greyboxaudio/Nyan-1073-EQ/eurorack_powerLayout.jpg

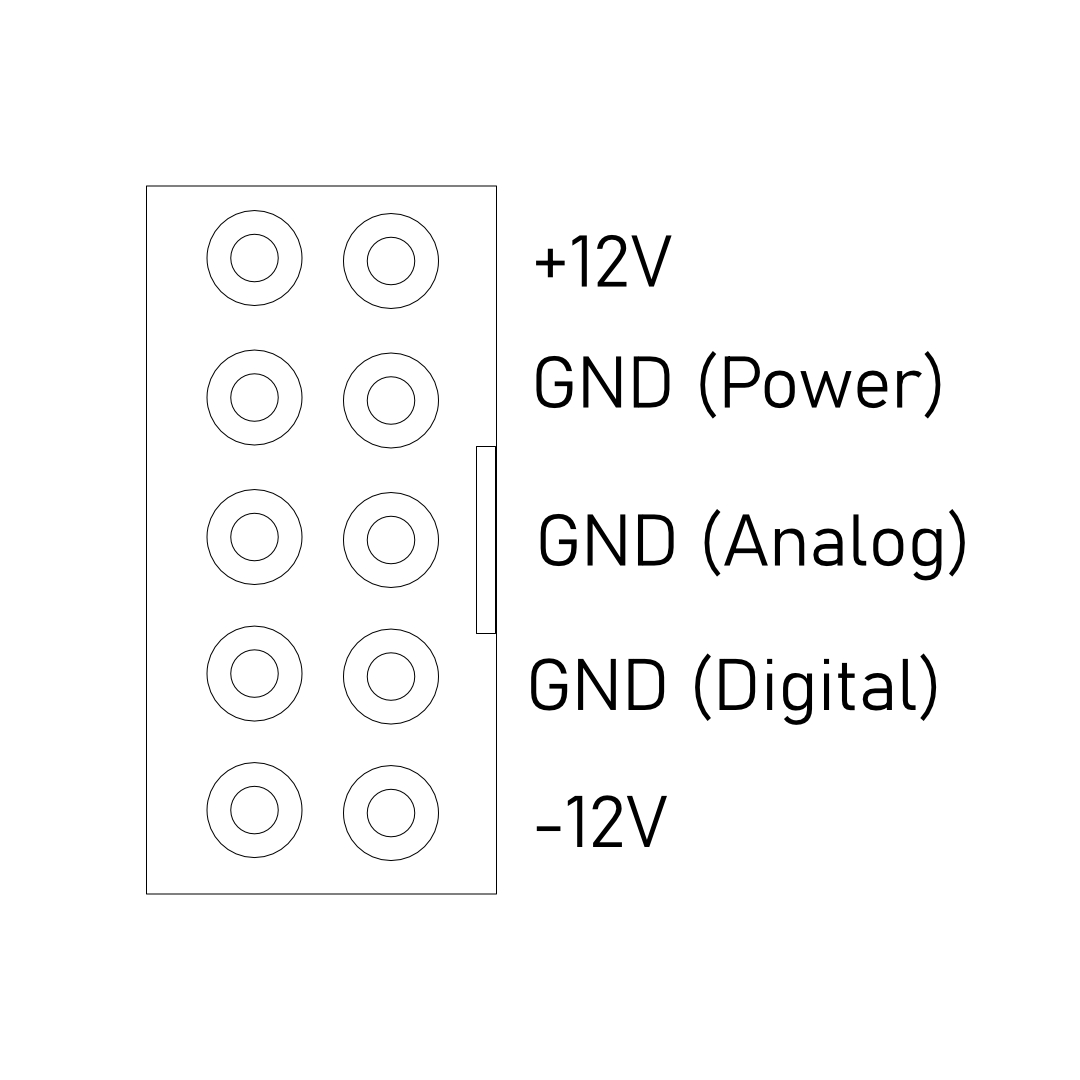
eurorack_powerLayout.jpg
