greyboxaudio/Nyan-1073-EQ/measurements/cheaps73_HP.jpg

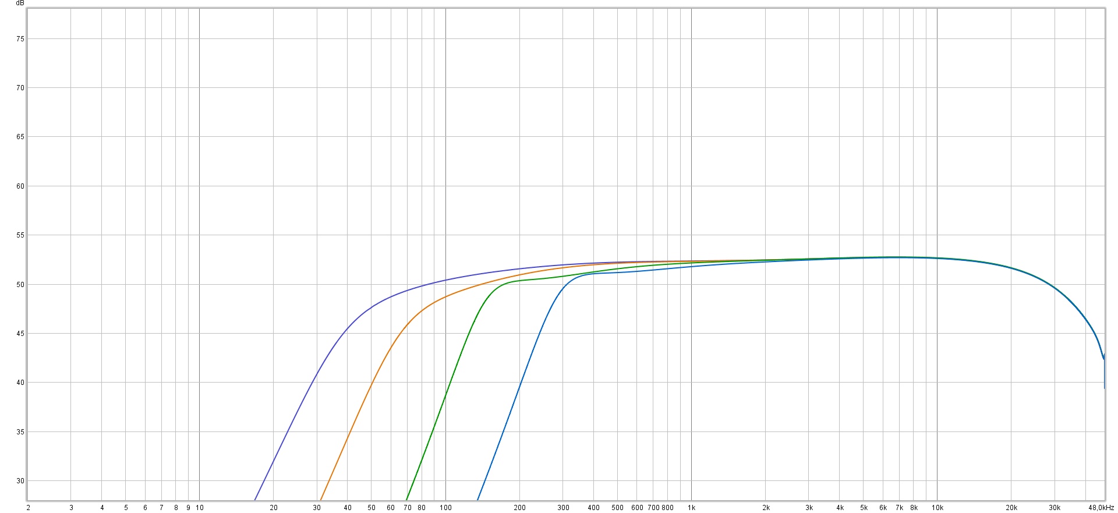
measurements/cheaps73_HP.jpg
