greyboxaudio/Nyan-1073-EQ/measurements/cheaps73_Low_High.jpg

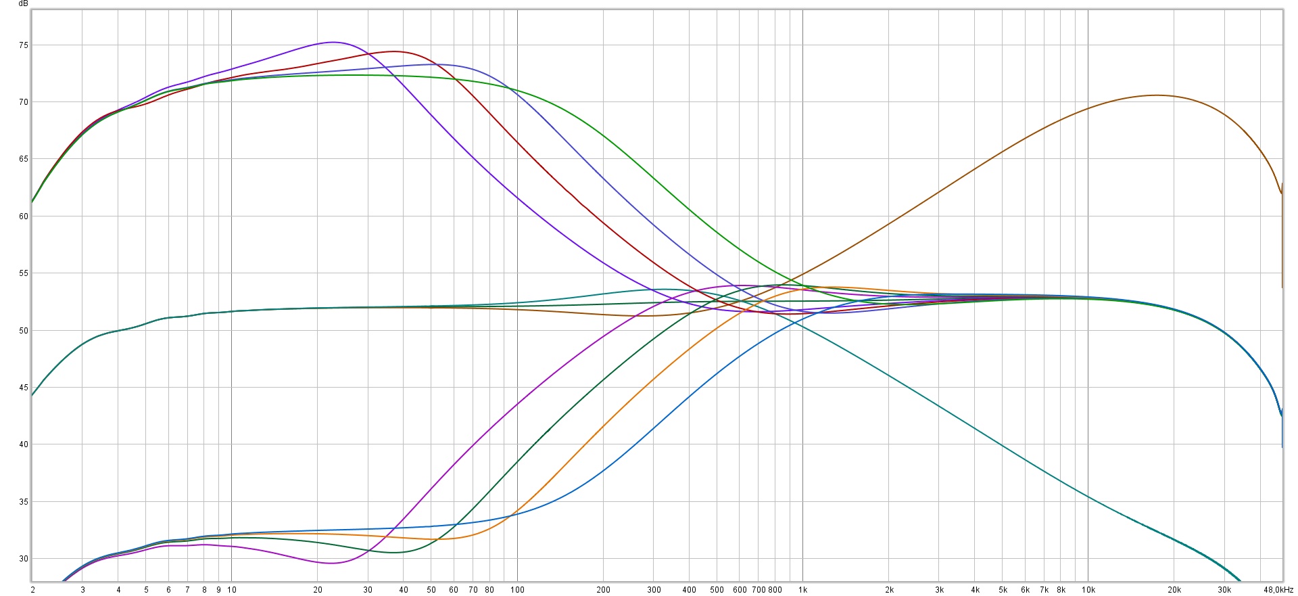
measurements/cheaps73_Low_High.jpg
