greyboxaudio/Nyan-1073-EQ/measurements/cheaps73_proportionalQ.jpg

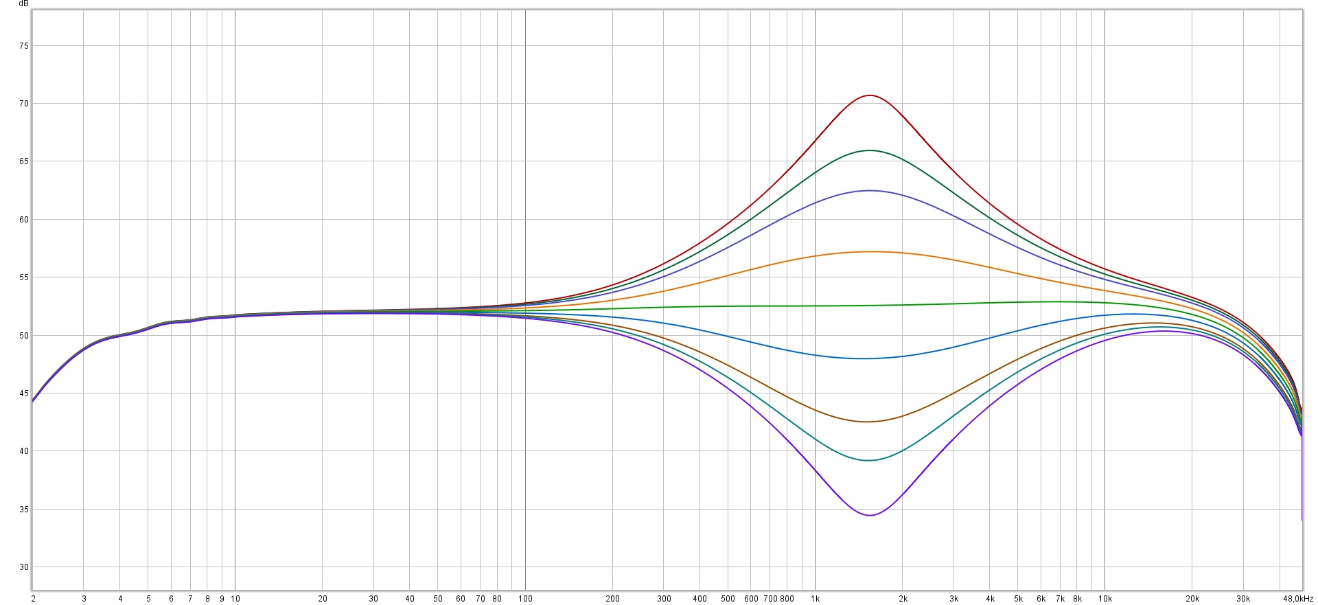
measurements/cheaps73_proportionalQ.jpg
