greyboxaudio/Nyan-1073-EQ/measurements/cheaps73_snr.jpg

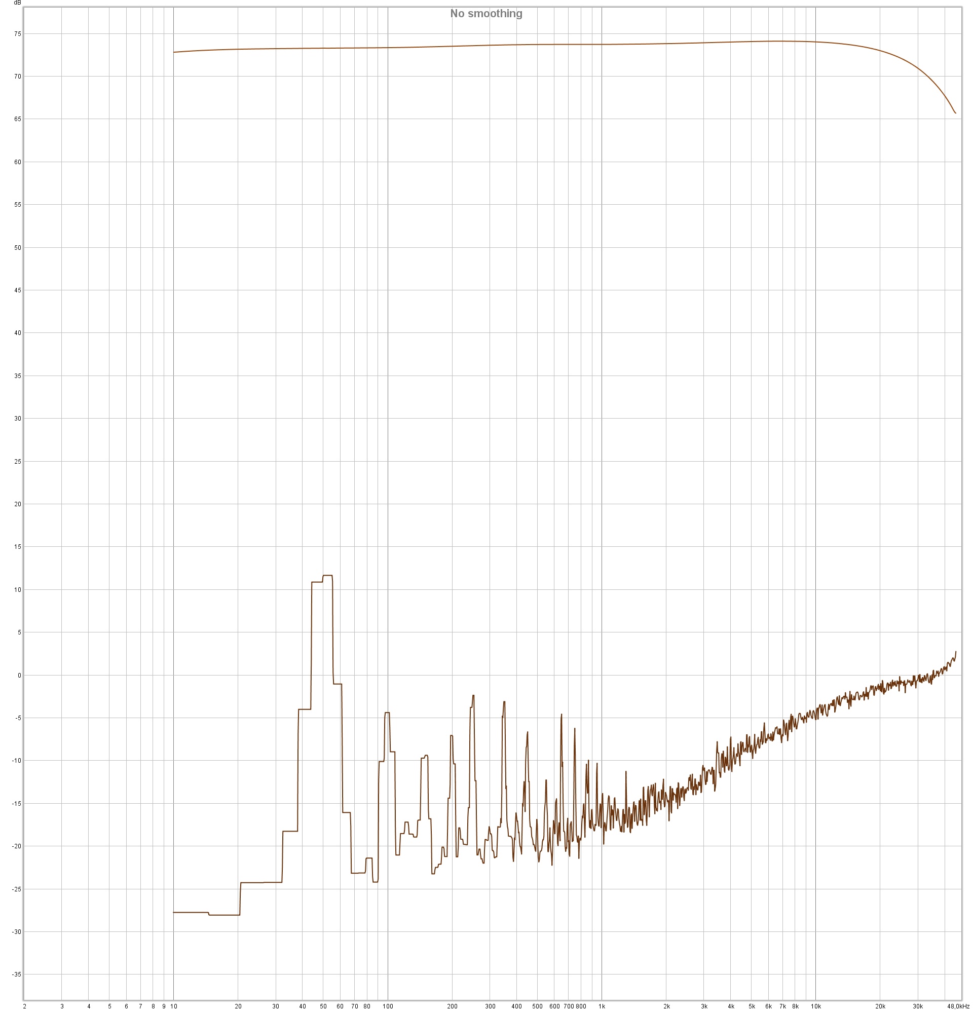
measurements/cheaps73_snr.jpg
