greyboxaudio/Nyan-1073-EQ/measurements/cheaps73_snr_reference.jpg

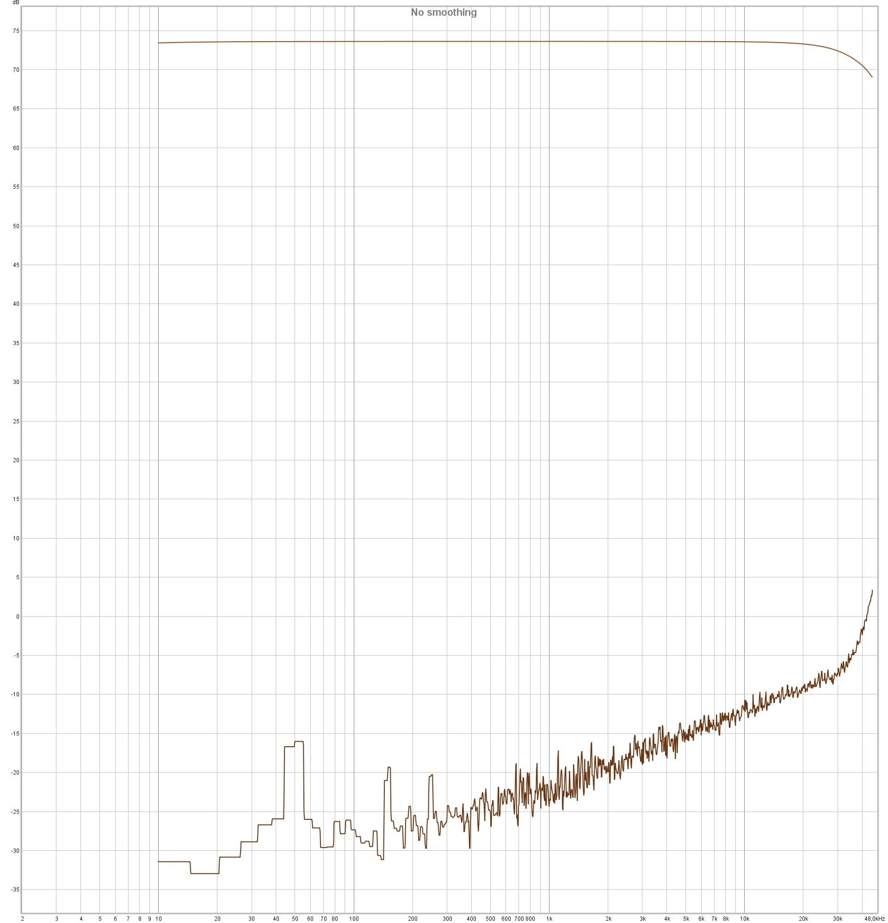
measurements/cheaps73_snr_reference.jpg
