greyboxaudio/Nyan-1073-EQ/measurements/nyan1073_hf.png

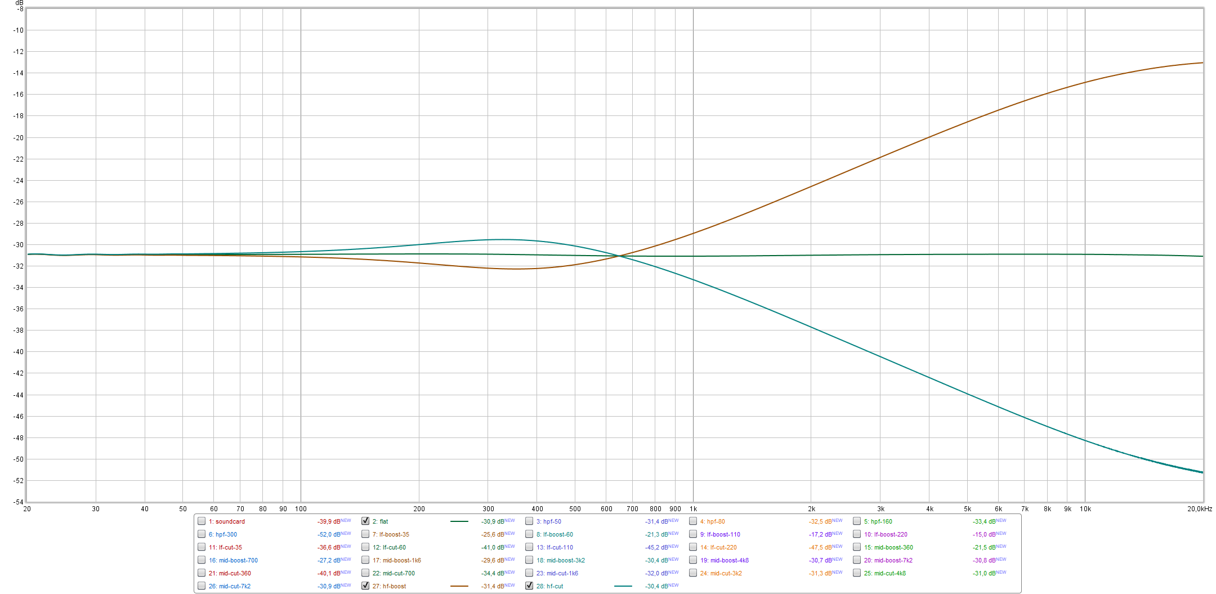
measurements/nyan1073_hf.png
