greyboxaudio/Nyan-1073-EQ/measurements/nyan1073_mid.png

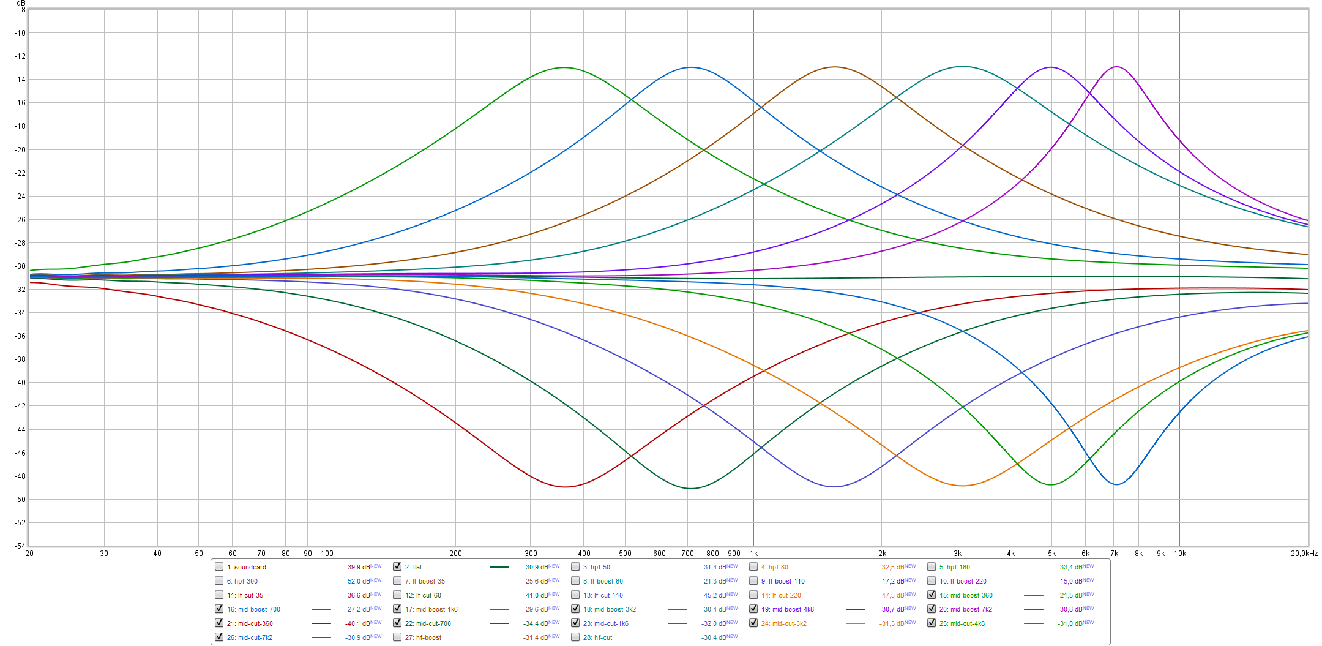
measurements/nyan1073_mid.png
