greyboxaudio/Nyan-1073-EQ/measurements/nyan1073_thdn.png

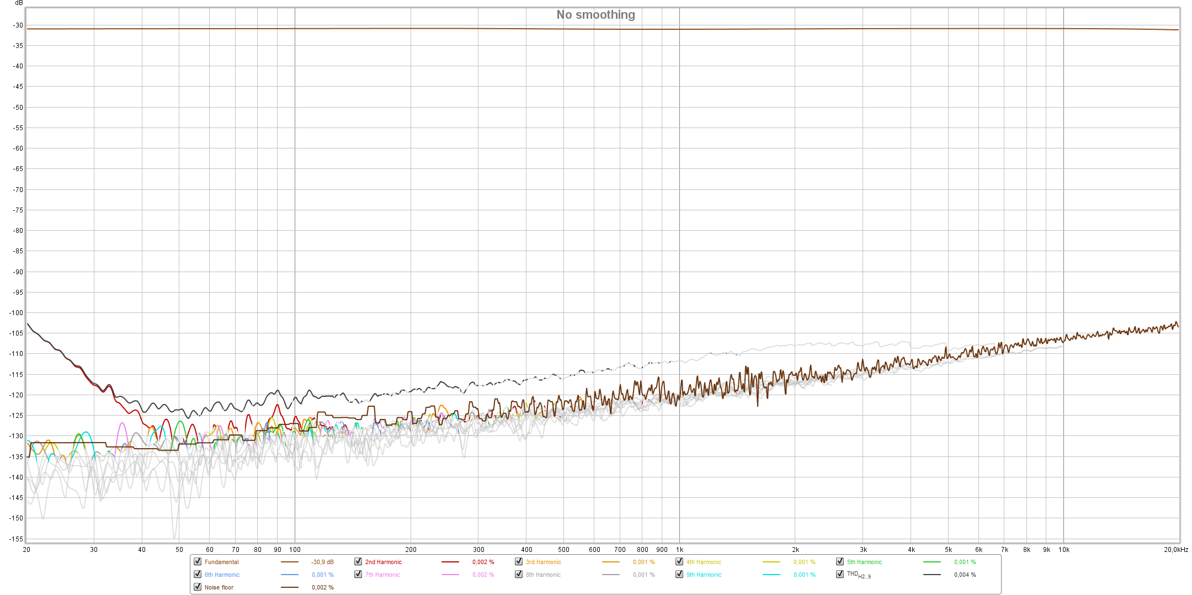
measurements/nyan1073_thdn.png
