greyboxaudio/Nyan-1073-EQ/NYAN_1073_v2.asc

C1: cap; 4n7; V=63
C2: cap; {Cn}; V=63
C3: cap; 22n
C4: cap; 10n
C5: cap; 22n
C6: cap; 15nf
C7: cap; 470p
C8: cap; 22µ
C9: cap; {C1}
C10: cap; {C1}
C11: cap; 10n; V=63
C12: cap; 0.22µ
C13: cap; 0.22µ
C14: cap; 68p
C15: cap; 0.22µ
C16: cap; 0.22µ
C17: cap; {Cg0}
C18: cap; {Cg2}
C19: cap; 68p
C20: cap; 1n
C21: cap; 22µ
C22: cap; 22µ
C23: cap; {Cg0}
C24: cap; 180p
C26: cap; {Cg1}
C27: cap; 4n7; V=63
C28: cap; 10n; V=63
C29: cap; 22µ
C30: cap; 180p
L1: ind; {Ln}; Rser=0
L2: ind; 3; Rser=490
R1: res; {R1}; tol=1 pwr=0.25
R2: res; {R2}; tol=1 pwr=0.25
R3: res; 23k
R4: res; 23k
R5: res; 2k7
R6: res; 6800; tol=1 pwr=0.25
R7: res; 6800; tol=1 pwr=0.25
R8: res; 1k
R9: res; 2700; tol=1 pwr=0.25
R10: res; 6800; tol=1 pwr=0.25
R11: res; {R4}
R12: res; {R3}
R13: res; 6800
R14: res; 620
R15: res; 620
R16: res; 12k
R17: res; 8200; tol=1 pwr=0.25
R18: res; 12k
R19: res; 6800; tol=1 pwr=0.25
R20: res; {R6}
R21: res; {R5}
R22: res; 470; tol=1 pwr=0.25
R23: res; 638k; tol=1 pwr=0.25
R24: res; 10k
R25: res; 5100
R26: res; 10k
R27: res; 8200; tol=1 pwr=0.25
R28: res; 6800; tol=1 pwr=0.25
R29: res; {R2}; tol=1 pwr=0.25
R30: res; {R1}; tol=1 pwr=0.25
R31: res; 10k
R32: res; 1200
R33: res; 5100
R34: res; 1k
R35: res; 1200
R36: res; {R1}; tol=1 pwr=0.25
R37: res; {R2}; tol=1 pwr=0.25
R38: res; 16800
R39: res; 16800
R40: res; 1200
R41: res; 10k
R42: res; 5100
R43: res; 10k
R44: res; {Rn}
R45: res; 20k
R46: res; 1k
R48: res; 10k
R49: res; 1k
R50: res; {R2}; tol=1 pwr=0.25
R51: res; {R1}; tol=1 pwr=0.25
R52: res; 10k
R53: res; 1200
R54: res; 5100
R55: res; 310; tol=1 pwr=0.25
R56: res; 60700; tol=1 pwr=0.25
R57: res; 1k8
U1: OP27
U2: OP27
U3: OP27
U4: ADTL082
U5: OP27
U6: ADTL082
U7: OP27
U8: OP27
U9: OP27
U10: ADTL082
U11: ADTL082
U12: ADTL082
V1: voltage; 12
V2: voltage; -12
V3: voltage; SINE(0 1 1000 0 0 0 1000); AC 1
Named nets: 0, V+, V-, gic, inductor, gyrator, gyrator_old
.ac dec 100 20 48k
;tran 0 250ms 230ms 0.0000762939453125
;noise V(gic)V3 oct 24 2 24k
Low Frequency
35Hz - 200n
 60 Hz - 100n
110Hz -  47n
220Hz -  15n
50 Hz -  10H / 1k / 1u
 80 Hz -    7H /800R / 470n
150Hz -   3H / 490R / 220n
300Hz - 1.3H /310R /122n
;step param Rx list 1 2 3 4 5
;param R1 table(Rx,1,1,2,2k,3,5k,4,8k,5,10k)
;param R2 table(Rx,1,10k,2,8k,3,5k,4,2k,5,1)
.param Ln=200m Rn=32 Cn=4n7
Neve
360Hz  - 2H / 85R / 100n
700 Hz - 1,1H / 59R / 47n
1,6kHz - 450mH / 35R / 22n
3,2kHz - 200mH / 32R / 12n2
4,8kHz - 200mH / 32R / 4n7
7,2kHz - 200mH / 32R / 2420p
.param Cg1=6n8 Cg2=150n
.param R1=10k R2=1 R3=5k R4=5k R5=25k R6=25k
.param Cg0=150p
RMS Noise (18dB @ 4,8kHz)
gyrator_2 = 174.04µV
inductor = 7.8711µV
gic = 23.708µV
gyrator = 45.948µV
.param C1=100n
Gyrator (standardized)
360Hz  - 150n / 1u5
700 Hz - 68n / 780n (680n + 100n)
1,6kHz -  33n / 330n
3,2kHz - 15n / 150n
4,8kHz - 6n8 / 150n
7,2kHz - 3n3 / 150n
;step param Cg0 list 82p 100p 150p 180p 220p
