greyboxaudio/Nyan-1073-EQ/cheaps_73.asc

C3: cap; 22n
C4: cap; 10n
C5: cap; 22n
C6: cap; 15nf
C7: cap; 470p
C9: cap; 47n
C10: cap; 47n
C11: cap; 100n; V=63
C12: cap; 0.22µ
C13: cap; 0.22µ
C14: cap; 2200p; V=63
C15: cap; 10n; V=63
C16: cap; 330p
R9: res; 10k
R10: res; 6200; tol=1 pwr=0.25
R11: res; 5k
R12: res; 5k
R13: res; 6200
R14: res; 620
R15: res; 620
R16: res; 12k
R17: res; 39k
R18: res; 12k
R20: res; 25k
R21: res; 25k
R22: res; 470; tol=1 pwr=0.25
R23: res; 63.8k; tol=1 pwr=0.25
R25: res; 5100
R26: res; 6800; tol=1 pwr=0.25
R27: res; 2700; tol=1 pwr=0.25
R28: res; 8200; tol=1 pwr=0.25
R29: res; 6800; tol=1 pwr=0.25
R30: res; 330; tol=1 pwr=0.25
R31: res; 60700; tol=1 pwr=0.25
R33: res; 5000; tol=1 pwr=0.25
R34: res; 10k
R35: res; 1200
R: res; 5000; tol=1 pwr=0.25
U3: ADTL082
U4: ADTL082
U5: ADTL082
U6: ADTL082
V1: voltage; 12
V2: voltage; -12
V3: voltage; SINE(0 1 1000 0 0 0 1000); AC 1
Named nets: 0, OUT, V+, V-
.ac dec 100 1 22000
;tran 0 250ms 230ms 0.0000762939453125
